levicole/fms-link/fms-link.kicad_sch

## KiCad design fms-link.kicad_sch (2026-09-19)

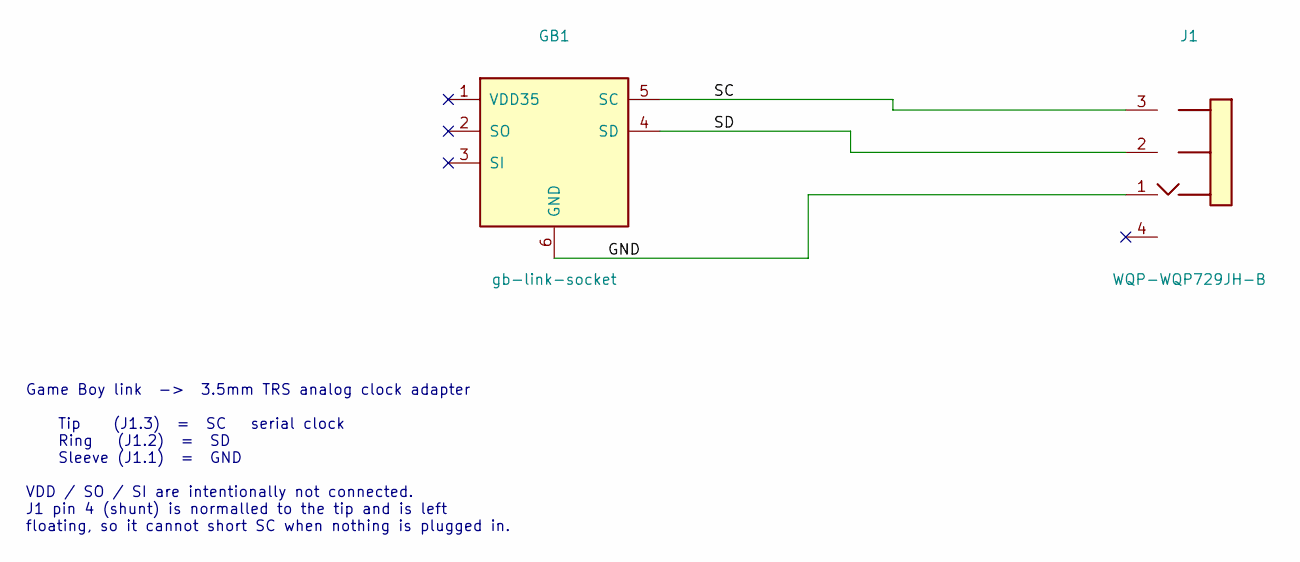
[picture p3: schematic fms-link.kicad_sch]

Parts:
GB1: gb-link-socket
J1: WQP-WQP729JH-B; Jack_3.5mm_QingPu_WQP-WQP729JH_Horizontal

Connections:
GND: GB1.6 (GND), J1.1 (Sleeve)
SC: GB1.5 (SC), J1.3 (Tip)
SD: GB1.4 (SD), J1.2 (Ring)

Notes on the sheet:
Game Boy link -> 3.5mm TRS analog clock adapter Tip (J1.3) = SC serial clock Ring (J1.2) = SD Sleeve (J1.1) = GND VDD / SO / SI are intentionally not connected. J1 pin 4 (shunt) is normalled to the tip and is left floating, so it cannot short SC when nothing is plugged in.
